SwiperWitty/PCB-MCU/Caven-3.14(NEW)/MCU/3D/B.png

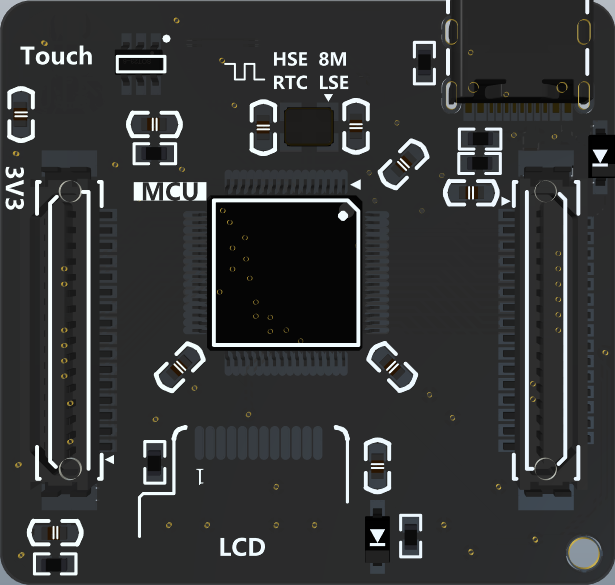
Caven-3.14(NEW)/MCU/3D/B.png
