SwiperWitty/PCB-MCU/Caven-3.14(NEW)/MCU/3D/F.png

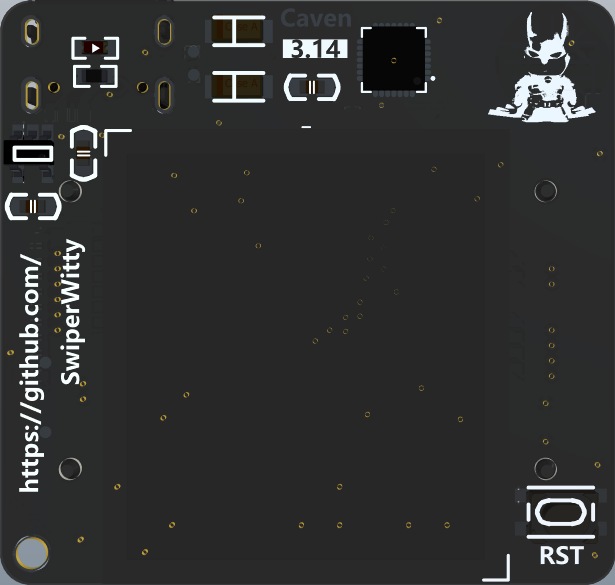
Caven-3.14(NEW)/MCU/3D/F.png
