SwiperWitty/PCB-MCU/Caven-3.14/1.jpg

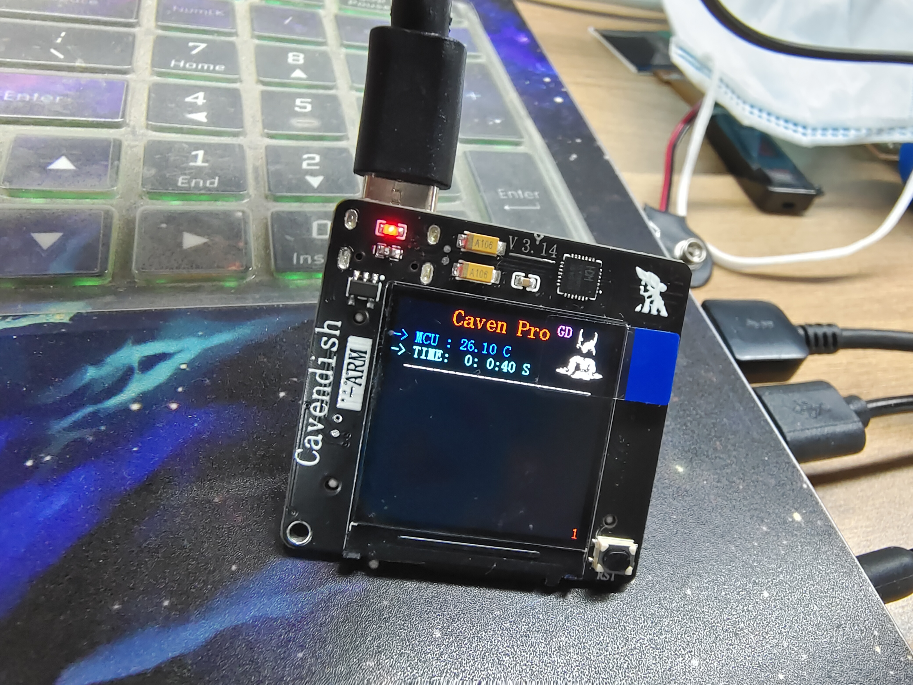
Caven-3.14/1.jpg
