SwiperWitty/PCB-MCU/Caven-3.14/4.png

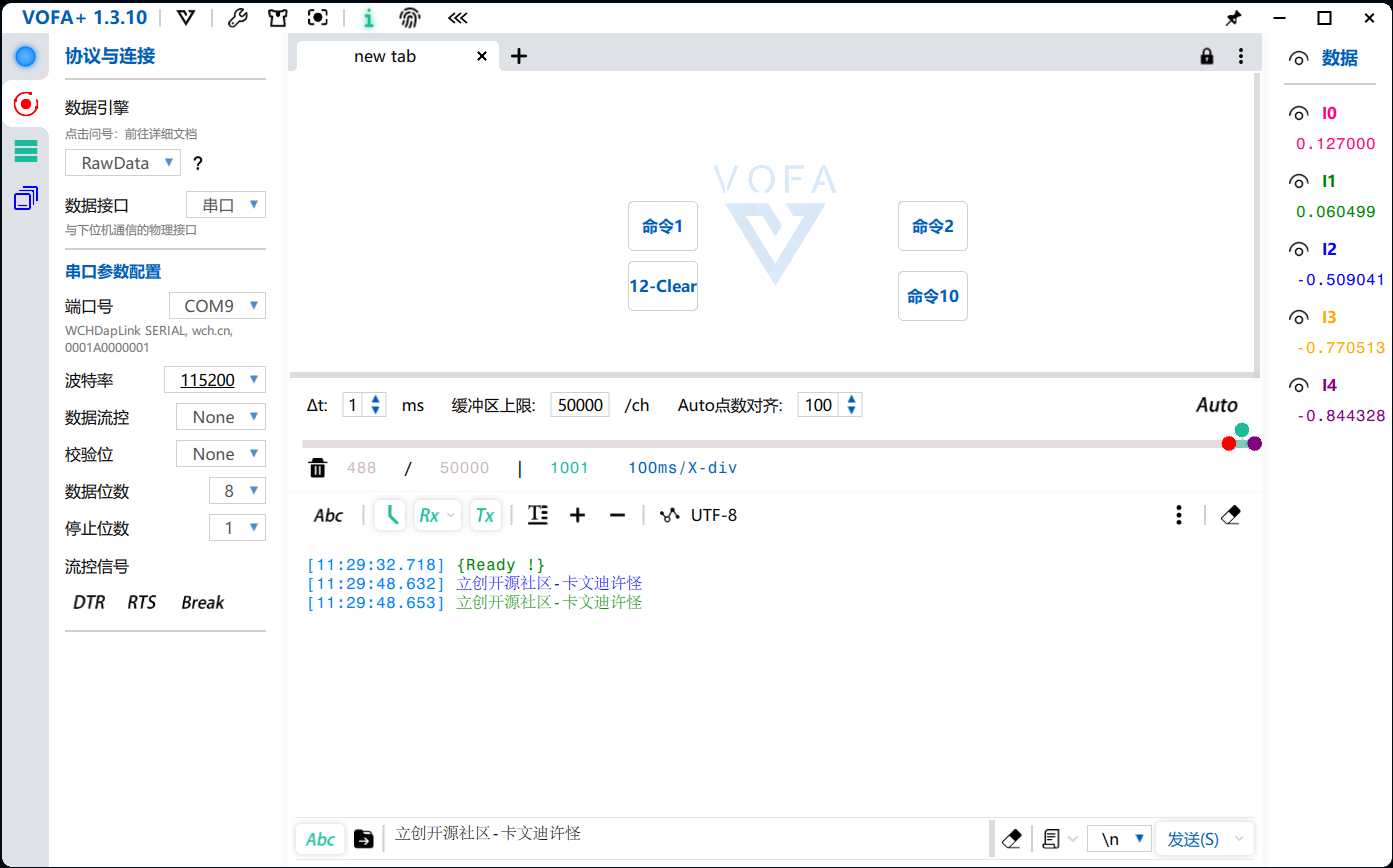
Caven-3.14/4.png
