SwiperWitty/PCB-MCU/Caven-3.14/5.png

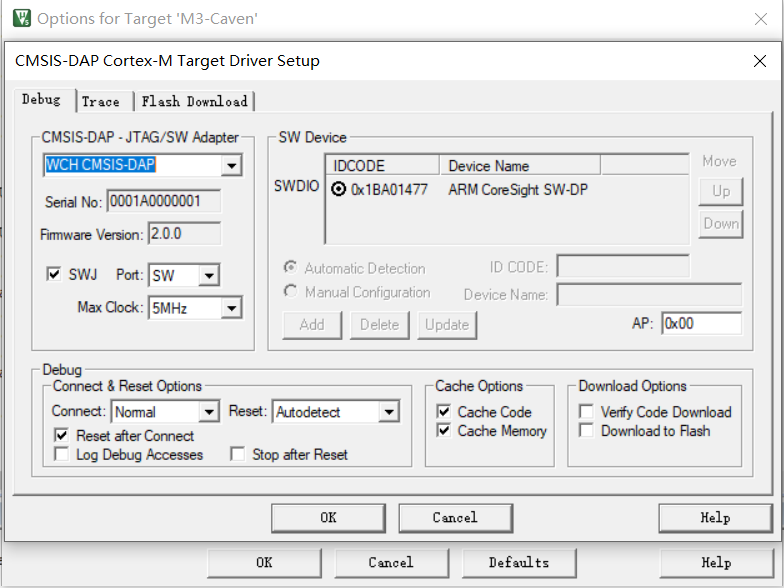
Caven-3.14/5.png
