SwiperWitty/PCB-MCU/ESP32-S3-HardWare/渲染/b.png

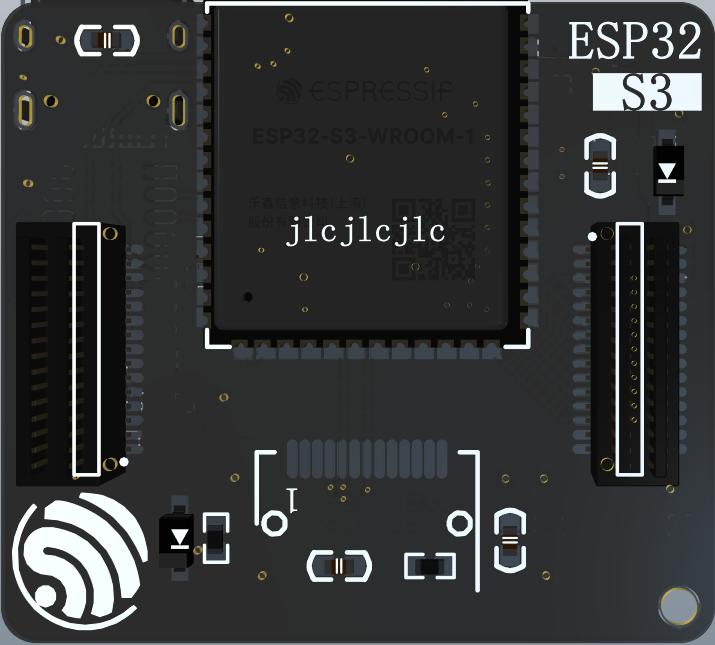
ESP32-S3-HardWare/渲染/b.png
