SwiperWitty/PCB-MCU/ESP32-S3-HardWare/渲染/bk.jpg

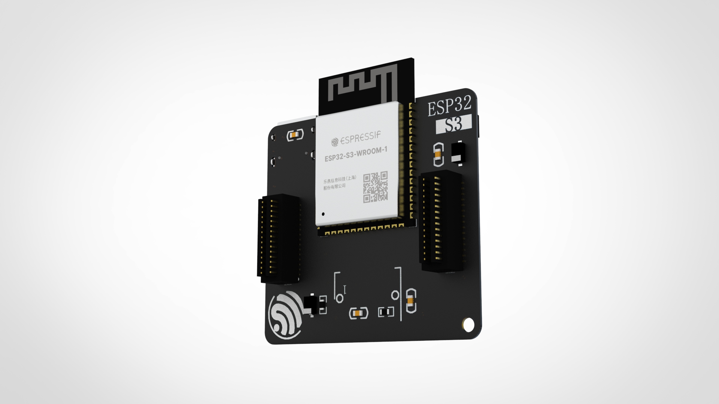
ESP32-S3-HardWare/渲染/bk.jpg
