SwiperWitty/PCB-MCU/ESP32-S3-HardWare/渲染/ft.jpg

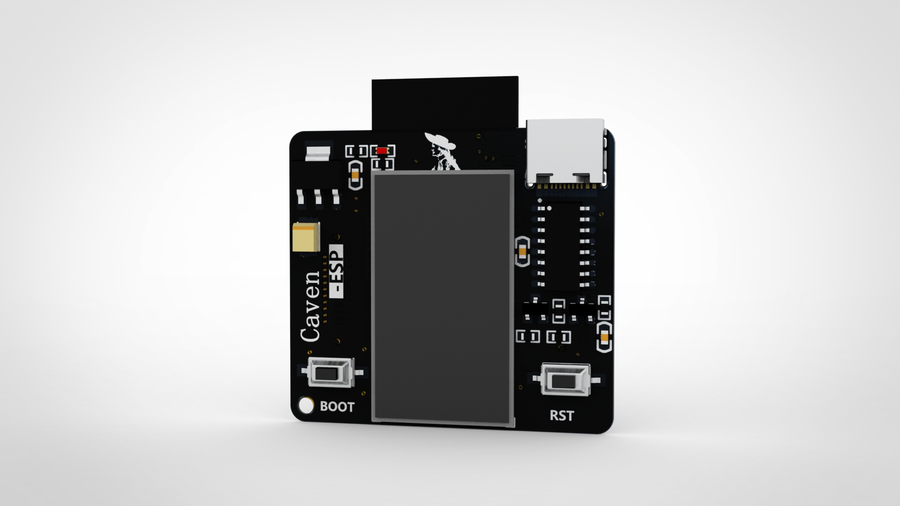
ESP32-S3-HardWare/渲染/ft.jpg
